PurkkaKoodari/ktane-hw/maincontroller/bombgame/bus/messages.py

from __future__ import annotations

import struct
from abc import ABC, abstractmethod
from enum import IntEnum

import can

from bombgame.events import BombErrorLevel
from bombgame.modules.registry import MODULE_ID_REGISTRY, MODULE_MESSAGE_ID_REGISTRY
from bombgame.utils import Registry, Ungettable, VersionNumber

MODULEID_TYPE_BITS = 12
MODULEID_SERIAL_BITS = 10
MODULEID_TYPE_MAX = (1 << MODULEID_TYPE_BITS) - 1
MODULEID_SERIAL_MAX = (1 << MODULEID_SERIAL_BITS) - 1


class ModuleId:
    """
    A module identifier as used on the bus.
    """

    BROADCAST: ModuleId

    def __init__(self, type_: int, serial: int):
        if not 0 <= type_ <= MODULEID_TYPE_MAX:
            raise ValueError(f"type must be between 0 and {MODULEID_TYPE_MAX}")
        if not 0 <= serial <= MODULEID_SERIAL_MAX:
            raise ValueError(f"serial must be between 0 and {MODULEID_SERIAL_MAX}")
        if type_ == 0 and serial != 0:
            raise ValueError("serial must be 0 if type is 0")
        self.type = type_
        self.serial = serial

    def is_broadcast(self):
        return self.type == 0

    def __int__(self):
        return (self.type << MODULEID_SERIAL_BITS) | self.serial

    def __eq__(self, other):
        return isinstance(other, ModuleId) and other.type == self.type and other.serial == self.serial

    def __hash__(self):
        return self.__int__()

    def __repr__(self):
        return f"ModuleId({self.type}, {self.serial})"

    def __str__(self):
        if self.type == 0:
            return "broadcast"
        if self.type in MODULE_ID_REGISTRY:
            return f"{MODULE_ID_REGISTRY[self.type].__name__}#{self.serial}"
        return f"{self.type}#{self.serial}"


ModuleId.BROADCAST = ModuleId(0, 0)


class BusMessageId(IntEnum):
    RESET = 0x00
    ANNOUNCE = 0x01
    INIT_COMPLETE = 0x02
    PING = 0x03
    LAUNCH_GAME = 0x10
    START_TIMER = 0x11
    EXPLODE = 0x12
    DEFUSE = 0x13
    STRIKE = 0x14
    SOLVE = 0x15
    NEEDY_ACTIVATE = 0x16
    NEEDY_DEACTIVATE = 0x17
    RECOVERABLE_ERROR = 0x20
    RECOVERED_ERROR = 0x21
    MINOR_UNRECOVERABLE_ERROR = 0x22
    MAJOR_UNRECOVERABLE_ERROR = 0x23
    MODULE_SPECIFIC_0 = 0x30
    MODULE_SPECIFIC_1 = 0x31
    MODULE_SPECIFIC_2 = 0x32
    MODULE_SPECIFIC_3 = 0x33
    MODULE_SPECIFIC_4 = 0x34
    MODULE_SPECIFIC_5 = 0x35
    MODULE_SPECIFIC_6 = 0x36
    MODULE_SPECIFIC_7 = 0x37
    MODULE_SPECIFIC_8 = 0x38
    MODULE_SPECIFIC_9 = 0x39
    MODULE_SPECIFIC_A = 0x3A
    MODULE_SPECIFIC_B = 0x3B
    MODULE_SPECIFIC_C = 0x3C
    MODULE_SPECIFIC_D = 0x3D
    MODULE_SPECIFIC_E = 0x3E
    MODULE_SPECIFIC_F = 0x3F


class BusMessageDirection(IntEnum):
    OUT = 0
    IN = 1


MESSAGE_DIRECTION_BITS = 1
MESSAGE_MODULE_TYPE_BITS = 12
MESSAGE_MODULE_SERIAL_BITS = 10
MESSAGE_ID_BITS = 6

MESSAGE_DIRECTION_OFFSET = 28
MESSAGE_MODULE_TYPE_OFFSET = 16
MESSAGE_MODULE_SERIAL_OFFSET = 6
MESSAGE_ID_OFFSET = 0

MESSAGE_DIRECTION_MASK = ((1 << MESSAGE_DIRECTION_BITS) - 1) << MESSAGE_DIRECTION_OFFSET
MESSAGE_MODULE_TYPE_MASK = ((1 << MESSAGE_MODULE_TYPE_BITS) - 1) << MESSAGE_MODULE_TYPE_OFFSET
MESSAGE_MODULE_SERIAL_MASK = ((1 << MESSAGE_MODULE_SERIAL_BITS) - 1) << MESSAGE_MODULE_SERIAL_OFFSET
MESSAGE_ID_MASK = ((1 << MESSAGE_ID_BITS) - 1) << MESSAGE_ID_OFFSET

MESSAGE_ID_REGISTRY = Registry("message_id")


class BusMessage(ABC):
    message_id = Ungettable

    def __init__(self, id_: BusMessageId, module: ModuleId, direction: BusMessageDirection = BusMessageDirection.OUT):
        if id_ < BusMessageId.MODULE_SPECIFIC_0 and MESSAGE_ID_REGISTRY[id_] != self.__class__:
            raise ValueError("incorrect message class for id")
        if module.is_broadcast() and direction != BusMessageDirection.OUT:
            raise ValueError("broadcast messages must be outward")

        self.id = id_
        self.module = module
        self.direction = direction

    @classmethod
    def parse(cls, message: can.Message) -> BusMessage:
        if not message.is_extended_id:
            raise ValueError("non-extended arbitration id")

        direction = (message.arbitration_id & MESSAGE_DIRECTION_MASK) >> MESSAGE_DIRECTION_OFFSET
        module_type = (message.arbitration_id & MESSAGE_MODULE_TYPE_MASK) >> MESSAGE_MODULE_TYPE_OFFSET
        module_serial = (message.arbitration_id & MESSAGE_MODULE_SERIAL_MASK) >> MESSAGE_MODULE_SERIAL_OFFSET
        message_id = (message.arbitration_id & MESSAGE_ID_MASK) >> MESSAGE_ID_OFFSET

        direction = BusMessageDirection(direction)
        module_id = ModuleId(module_type, module_serial)

        if message_id >= BusMessageId.MODULE_SPECIFIC_0:
            if module_id.type not in MODULE_ID_REGISTRY:
                raise ValueError(f"unknown module type {hex(module_id.type)}")
            module_type = MODULE_ID_REGISTRY[module_id.type]
            lookup = (module_type, message_id)
            if lookup not in MODULE_MESSAGE_ID_REGISTRY:
                raise ValueError(f"unknown message id {hex(message_id)} for {module_type.__name__}")
            message_class = MODULE_MESSAGE_ID_REGISTRY[lookup]
        else:
            if message_id not in MESSAGE_ID_REGISTRY:
                raise ValueError(f"unknown message id {hex(message_id)}")
            message_class = MESSAGE_ID_REGISTRY[message_id]

        return message_class._parse_data(module_id, direction, message.data)

    def serialize(self) -> can.Message:
        arbitration_id = ((self.direction << MESSAGE_DIRECTION_OFFSET)
                          | (self.module.type << MESSAGE_MODULE_TYPE_OFFSET)
                          | (self.module.serial << MESSAGE_MODULE_SERIAL_OFFSET)
                          | (self.id << MESSAGE_ID_OFFSET))
        data = self._serialize_data()
        return can.Message(arbitration_id=arbitration_id, is_extended_id=True, data=data, check=True)

    @classmethod
    @abstractmethod
    def _parse_data(cls, module: ModuleId, direction: BusMessageDirection, data: bytes) -> BusMessage:
        pass

    @abstractmethod
    def _serialize_data(self) -> bytes:
        pass

    def __repr__(self):
        data_repr = self._data_repr()
        data_repr = f": {data_repr}" if data_repr else ""
        direction = "to" if self.direction == BusMessageDirection.OUT else "from"
        return f"<{self.__class__.__name__} {direction} {self.module}{data_repr}>"

    @abstractmethod
    def _data_repr(self) -> str:
        pass


class SimpleBusMessage(BusMessage):
    def __init__(self, module: ModuleId, direction: BusMessageDirection = BusMessageDirection.OUT):
        super().__init__(self.__class__.message_id, module, direction)

    @classmethod
    def _parse_data(cls, module: ModuleId, direction: BusMessageDirection, data: bytes):
        if data:
            raise ValueError(f"no data allowed for {cls.__name__}")
        return cls(module, direction)

    def _serialize_data(self):
        return b""

    def _data_repr(self):
        return ""


class StatusMessage(SimpleBusMessage):
    pass


class BombStatusMessage(StatusMessage):
    pass


class ModuleStatusMessage(StatusMessage):
    pass


class ErrorMessage(StatusMessage):
    error_level = Ungettable

    def __init__(self, module: ModuleId, direction: BusMessageDirection = BusMessageDirection.OUT, *, code: int, details: bytes):
        super().__init__(module, direction)
        if len(details) > 7:
            raise ValueError("error details must be up to 7 bytes")
        self.code = code
        self.details = details

    @classmethod
    def _parse_data(cls, module: ModuleId, direction: BusMessageDirection, data: bytes):
        if not 1 <= len(data) <= 8:
            raise ValueError(f"{cls.__name__} must have 1 to 8 bytes of data")
        code, = struct.unpack_from("<B", data, 0)
        return cls(module, direction, code=code, details=data[1:])

    def _serialize_data(self):
        return struct.pack("<B", self.code) + self.details


@MESSAGE_ID_REGISTRY.register
class ResetMessage(SimpleBusMessage):
    message_id = BusMessageId.RESET


@MESSAGE_ID_REGISTRY.register
class AnnounceMessage(BusMessage):
    message_id = BusMessageId.ANNOUNCE

    FLAG_INIT_COMPLETE = 0x01

    def __init__(self, module: ModuleId, direction: BusMessageDirection = BusMessageDirection.OUT, *,
                 hw_version: VersionNumber, sw_version: VersionNumber, init_complete: bool):
        super().__init__(self.__class__.message_id, module, direction)
        self.hw_version = hw_version
        self.sw_version = sw_version
        self.init_complete = init_complete

    @classmethod
    def _parse_data(cls, module: ModuleId, direction: BusMessageDirection, data: bytes):
        if len(data) != 5:
            raise ValueError(f"{cls.__name__} must have 5 bytes of data")
        hw_major, hw_minor, sw_major, sw_minor, flags = struct.unpack("<BBBBB", data)
        init_complete = bool(flags & AnnounceMessage.FLAG_INIT_COMPLETE)
        return cls(module, direction, hw_version=VersionNumber(hw_major, hw_minor),
                   sw_version=VersionNumber(sw_major, sw_minor), init_complete=init_complete)

    def _serialize_data(self):
        flags = AnnounceMessage.FLAG_INIT_COMPLETE * self.init_complete
        return struct.pack("<BBBBB", *self.hw_version, *self.sw_version, flags)

    def _data_repr(self):
        completeness = "complete" if self.init_complete else "incomplete"
        return f"hardware {self.hw_version}, software {self.sw_version}, init {completeness}"


@MESSAGE_ID_REGISTRY.register
class InitCompleteMessage(SimpleBusMessage):
    message_id = BusMessageId.INIT_COMPLETE


@MESSAGE_ID_REGISTRY.register
class PingMessage(BusMessage):
    message_id = BusMessageId.PING

    def __init__(self, module: ModuleId, direction: BusMessageDirection = BusMessageDirection.OUT, *, number: int = 0):
        super().__init__(self.__class__.message_id, module, direction)
        if not 0 <= number <= 0xFF:
            raise ValueError("ping number must be a byte")
        self.number = number

    @classmethod
    def _parse_data(cls, module: ModuleId, direction: BusMessageDirection, data: bytes) -> BusMessage:
        if len(data) > 1:
            raise ValueError(f"{cls.__name__} must have 0 or 1 bytes of data")
        number, = struct.unpack("<B", data) if data else (0,)
        return cls(module, direction, number=number)

    def _serialize_data(self) -> bytes:
        return struct.pack("<B", self.number)

    def _data_repr(self) -> str:
        return f"id {self.number}"


@MESSAGE_ID_REGISTRY.register
class LaunchGameMessage(BombStatusMessage):
    message_id = BusMessageId.LAUNCH_GAME


@MESSAGE_ID_REGISTRY.register
class StartTimerMessage(BombStatusMessage):
    message_id = BusMessageId.START_TIMER


@MESSAGE_ID_REGISTRY.register
class ExplodeBombMessage(BombStatusMessage):
    message_id = BusMessageId.EXPLODE


@MESSAGE_ID_REGISTRY.register
class DefuseBombMessage(BombStatusMessage):
    message_id = BusMessageId.DEFUSE


@MESSAGE_ID_REGISTRY.register
class StrikeModuleMessage(ModuleStatusMessage):
    message_id = BusMessageId.STRIKE


@MESSAGE_ID_REGISTRY.register
class SolveModuleMessage(ModuleStatusMessage):
    message_id = BusMessageId.SOLVE


@MESSAGE_ID_REGISTRY.register
class NeedyActivateMessage(ModuleStatusMessage):
    message_id = BusMessageId.NEEDY_ACTIVATE


@MESSAGE_ID_REGISTRY.register
class NeedyDeactivateMessage(ModuleStatusMessage):
    message_id = BusMessageId.NEEDY_DEACTIVATE


@MESSAGE_ID_REGISTRY.register
class RecoverableErrorMessage(ErrorMessage):
    message_id = BusMessageId.RECOVERABLE_ERROR
    error_level = BombErrorLevel.RECOVERABLE


@MESSAGE_ID_REGISTRY.register
class RecoveredErrorMessage(ErrorMessage):
    message_id = BusMessageId.RECOVERED_ERROR
    error_level = BombErrorLevel.RECOVERED


@MESSAGE_ID_REGISTRY.register
class MinorUnrecoverableErrorMessage(ErrorMessage):
    message_id = BusMessageId.MINOR_UNRECOVERABLE_ERROR
    error_level = BombErrorLevel.MINOR


@MESSAGE_ID_REGISTRY.register
class MajorUnrecoverableErrorMessage(ErrorMessage):
    message_id = BusMessageId.MAJOR_UNRECOVERABLE_ERROR
    error_level = BombErrorLevel.MAJOR
