PurkkaKoodari/ktane-hw/module/password_genfont.prebuild.py

from os.path import dirname, abspath, join

font = {
0x00:"""







""",
0x01:"""
#####
#####
#####
#####
#####
#####
#####
""",
0x02:"""
# # #
# # #
# # #
# # #
# # #
# # #
# # #
""",
0x03:"""
 # # 
 # # 
 # # 
 # # 
 # # 
 # # 
 # # 
""",
0x04:"""
#####
     
#####
     
#####
     
#####
""",
0x05:"""
     
#####
     
#####
     
#####
     
""",
" ":"""







""",
"!":"""
  #
  #
  #
  #
  #

  #
""",
'"':"""

 # #
#####
 # #
 # #
#####
 # #
""",
"$":"""
  #
 ####
# #
 ###
  # #
####
  #
""",
"%":"""
##
##  #
   #
  #
 #
#  ##
   ##
""",
"&":"""
 ##
#
# #
 #
# # #
#  #
 ## #
""",
"'":"""
  #
  #





""",
"(":"""
   #
  #
 #
 #
 #
  #
   #
""",
")":"""
 #
  #
   #
   #
   #
  #
 #
""",
"*":"""
  #
# # #
 ###
# # #
  #


""",
"+":"""

  #
  #
#####
  #
  #

""",
",":"""





  #
 #
""",
"-":"""



#####



""",
".":"""






  #
""",
"/":"""
    #
    #
   #
  #
 #
#
#
""",
"0":"""
 ###
##  #
# # #
# # #
# # #
#  ##
 ###
""",
"1":"""
  #
 ##
# #
  #
  #
  #
#####
""",
"2":"""
 ###
#   #
   #
  #
 #
#
#####
""",
"3":"""
 ###
#   #
    #
  ##
    #
#   #
 ###
""",
"4":"""
#   #
#   #
#   #
#####
    #
    #
    #
""",
"5":"""
#####
#
####
    #
    #
#   #
 ###
""",
"6":"""
 ###
#   #
#
####
#   #
#   #
 ###
""",
"7":"""
#####
    #
    #
   #
   #
  #
  #
""",
"8":"""
 ###
#   #
#   #
 ###
#   #
#   #
 ###
""",
"9":"""
 ###
#   #
#   #
 ####
    #
#   #
 ###
""",
":":"""

  #



  #

""",
";":"""

  #



  #
 #
""",
"<":"""

   ##
 ##
#
 ##
   ##

""",
"=":"""


#####

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
  #
  #
##
""",
"~":"""


 #
# # #
   #


""",
"Å":"""
  #

  #
 # #
#   #
#####
#   #
""",
"Ä":"""
#   #

  #
 # #
#   #
#####
#   #
""",
"Ö":"""
#   #

 ###
#   #
#   #
#   #
 ###
""",
"å":"""
  #

 ###
    #
 ####
#   #
 ####
""",
"ä":"""
#   #

 ###
    #
 ####
#   #
 ####
""",
"ö":"""
#   #

 ###
#   #
#   #
#   #
 ###
""",
}

row_order = [2, 4, 5, 6, 3, 1, 0]
col_order = [0, 1, 3, 4, 2]

# default to empty symbol
fontmap = [[0] * 5 for _ in range(256)]

for char, glyph in font.items():
    pos = ord(char) if isinstance(char, str) else char
    # expand lines to 5 cols
    lines = [line.ljust(5) for line in glyph.splitlines()[1:]]
    # sanity checks
    assert sum(fontmap[pos]) == 0, f"duplicate glyph for {repr(char)}"
    assert len(lines) == 7, f"too high/low glyph for {repr(char)}"
    assert all(len(line) == 5 for line in lines), f"too wide glyph for {repr(char)}"
    # find non-spaces
    lines = [[not char.isspace() for char in line] for line in lines]
    # reorder columns
    lines = [[line[col_order[i]] for i in range(5)] for line in lines]
    # reorder lines
    lines = [lines[row_order[i]] for i in range(7)]
    # transpose
    cols = [[lines[j][i] for j in range(7)] for i in range(5)]
    # convert to ints
    cols = [sum(bit << i for i, bit in enumerate(col)) for col in cols]
    # add to map
    fontmap[pos] = cols

firmware_folder = dirname(abspath(__file__))
output_file = join(firmware_folder, "password_font.gen.cpp")

with open(output_file, "w") as stream:
    stream.write('#include "module.h"\n')
    stream.write("#if MODULE_TYPE == MODULE_TYPE_PASSWORD\n")
    stream.write('#include "password_font.h"\n')
    stream.write("\n")
    stream.write("const uint8_t font[256][5] PROGMEM = {\n")
    for glyph in fontmap:
        stream.write("    {" + ", ".join(hex(col) for col in glyph) + "},\n")
    stream.write("};\n")
    stream.write("#endif\n")
