PurkkaKoodari/ktane-hw/module/timer.cpp

#include "timer.h"

#if MODULE_TYPE == MODULE_TYPE_TIMER

struct timer_tick_data {
  uint16_t time_left;
  uint16_t timer_speed;
  uint8_t strikes;
  uint8_t max_strikes;
};

unsigned long last_tick;
uint16_t seconds_left;
uint16_t timer_speed;
uint8_t strikes;
uint8_t max_strikes;

#if VERSION_HW_MAJOR == 0
HT1632 matrix(HT1632_DATA_PIN, HT1632_WR_PIN, HT1632_CS_PIN, 5, 8);
#elif VERSION_HW_MAJOR == 1
Adafruit_LEDBackpack matrix = Adafruit_LEDBackpack();
#endif

const uint8_t digits_7seg[10] = {
#if VERSION_HW_MAJOR == 0
//  gfedcba
  0b0111111,
  0b0000110,
  0b1011011,
  0b1001111,
  0b1100110,
  0b1101101,
  0b1111101,
  0b0000111,
  0b1111111,
  0b1101111
#elif VERSION_HW_MAJOR == 1
//  ed.cgbfa
  0b11010111,
  0b00010100,
  0b11001101,
  0b01011101,
  0b00011110,
  0b01011011,
  0b11011011,
  0b00010101,
  0b11011111,
  0b01011111,
#endif
};

void moduleInitHardware() {
#if VERSION_HW_MAJOR == 0
  matrix.begin();
  delay(50);
  matrix.clear();
  matrix.update();
#elif VERSION_HW_MAJOR == 1
  matrix.begin(0x70);
#endif
  digitalWrite(STRIKE_1_PIN, HIGH);
  pinMode(STRIKE_1_PIN, OUTPUT);
  digitalWrite(STRIKE_2_PIN, HIGH);
  pinMode(STRIKE_2_PIN, OUTPUT);
}

void moduleReset() {
  seconds_left = 0xffff;
  timer_speed = 0;
  strikes = 0;
  max_strikes = 3;
}

void moduleStartTimer() {
  last_tick = millis();
}

bool moduleHandleMessage(uint16_t messageId) {
  switch (messageId) {
  case MESSAGE_MODULE_SPECIFIC_0:
    last_tick = millis();
    seconds_left = ((struct timer_tick_data *) &canFrame.data)->time_left;
    timer_speed = ((struct timer_tick_data *) &canFrame.data)->timer_speed;
    strikes = ((struct timer_tick_data *) &canFrame.data)->strikes;
    max_strikes = ((struct timer_tick_data *) &canFrame.data)->max_strikes;
    DEBUG_PRINT("updated secs ");
    DEBUG_PRINT(seconds_left);
    DEBUG_PRINT(" speed ");
    DEBUG_PRINTLN(timer_speed);
    return true;
  default:
    return false;
  }
}

void moduleLoop() {
  if (mode == CONFIGURATION || mode == GAME) {
    if (exploded) {
#if VERSION_HW_MAJOR == 0
      matrix.clear();
      matrix.update();
#elif VERSION_HW_MAJOR == 1
      matrix.clear();
      matrix.writeDisplay();
#endif
      digitalWrite(STRIKE_1_PIN, HIGH);
      digitalWrite(STRIKE_2_PIN, HIGH);
    } else {
      if (seconds_left == 0xffff) {
#if VERSION_HW_MAJOR == 0
        matrix.clear();
        matrix.set(0, 6, true);
        matrix.set(1, 6, true);
        matrix.set(2, 6, true);
        matrix.set(3, 6, true);
        matrix.set(4, 7, true);
#elif VERSION_HW_MAJOR == 1
        matrix.displaybuffer[0] = 0;
        matrix.displaybuffer[1] = 0;
        matrix.displaybuffer[2] = 0;
        matrix.displaybuffer[3] = 0b1111;
        matrix.displaybuffer[4] = 0;
        matrix.displaybuffer[5] = 0b10000;
        matrix.displaybuffer[6] = 0;
        matrix.displaybuffer[7] = 0;
#endif
      } else {
        uint16_t real_speed = mode == GAME && timer_started && !game_ended ? timer_speed : 0;
        signed long centis_elapsed = (signed long) ((millis() - last_tick) * real_speed / 2560);
        signed long centis_left = 100 * (signed long) seconds_left - centis_elapsed;
        if (centis_left < 0) {
          centis_left = 0;
        }
        uint8_t digits[4];
        if (centis_left < 6000) {
          uint8_t secs = (uint8_t) (centis_left / 100);
          uint8_t centis = (uint8_t) (centis_left % 100);
          digits[0] = digits_7seg[secs / 10];
          digits[1] = digits_7seg[secs % 10];
          digits[2] = digits_7seg[centis / 10];
          digits[3] = digits_7seg[centis % 10];
        } else {
          uint8_t mins = (uint8_t) (centis_left / 6000);
          uint8_t secs = (uint8_t) (centis_left / 100 % 60);
          digits[0] = digits_7seg[mins / 10];
          digits[1] = digits_7seg[mins % 10];
          digits[2] = digits_7seg[secs / 10];
          digits[3] = digits_7seg[secs % 10];
        }
        bool colon_on = centis_elapsed % 100 >= 50;
#if VERSION_HW_MAJOR == 0
        for (uint8_t i = 0; i < 4; i++) {
          for (uint8_t j = 0; j < 7; j++) {
            matrix.set(i, j, (digits[i] >> j) & 1);
          }
        }
        matrix.set(4, 7, colon_on);
#elif VERSION_HW_MAJOR == 1
        matrix.clear();
        for (uint8_t i = 0; i < 8; i++) {
          uint16_t segs = 0;
          for (uint8_t j = 0; j < 4; j++) {
            segs |= ((digits[j] >> i) & 1) << j;
          }
          matrix.displaybuffer[i] = segs;
        }
        matrix.displaybuffer[5] |= colon_on << 4;
#endif
      }
#if VERSION_HW_MAJOR == 0
      matrix.update();
#elif VERSION_HW_MAJOR == 1
      matrix.writeDisplay();
#endif
      if (strikes == 0) {
        digitalWrite(STRIKE_1_PIN, HIGH);
        digitalWrite(STRIKE_2_PIN, HIGH);
      } else if (strikes == 1) {
        digitalWrite(STRIKE_1_PIN, LOW);
        digitalWrite(STRIKE_2_PIN, HIGH);
      } else {
        bool state = millis() % 200 < 100 ? HIGH : LOW;
        digitalWrite(STRIKE_1_PIN, state);
        digitalWrite(STRIKE_2_PIN, state);
      }
    }
  }
}

#endif
