PurkkaKoodari/ktane-hw/module/simon.h

#include "module.h"

#if MODULE_TYPE == MODULE_TYPE_SIMON_SAYS

#if VERSION_HW_MAJOR != 1 || VERSION_HW_MINOR != 0
#error This version of the module software does not support the configured hardware version.
#endif

#define VERSION_SW_MAJOR 1
#define VERSION_SW_MINOR 0

#define MODULE_NAME "Simon Says"

#define LED_BLUE_PIN 10
#define LED_YELLOW_PIN 6
#define LED_GREEN_PIN 5
#define LED_RED_PIN 9
#define BUTTON_BLUE_PIN 3
#define BUTTON_YELLOW_PIN 4
#define BUTTON_GREEN_PIN A4
#define BUTTON_RED_PIN 7

#define STRIKE_LED_PIN A0
#define SOLVE_LED_PIN A1

#endif
